lucacros/2324_Projet2A_PedaleGuitare/Hardware/img/att.ZSk6oNu2TNIRMZUWemjoR3e5RhZ518ov_QuzrdiQLX0.jpg

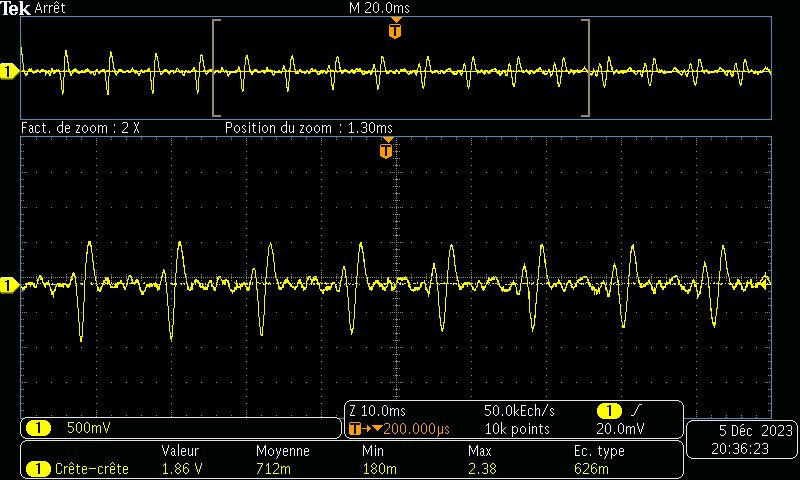
Hardware/img/att.ZSk6oNu2TNIRMZUWemjoR3e5RhZ518ov_QuzrdiQLX0.jpg
