lucacros/2324_Projet2A_PedaleGuitare/Hardware/img/Buffer button.png

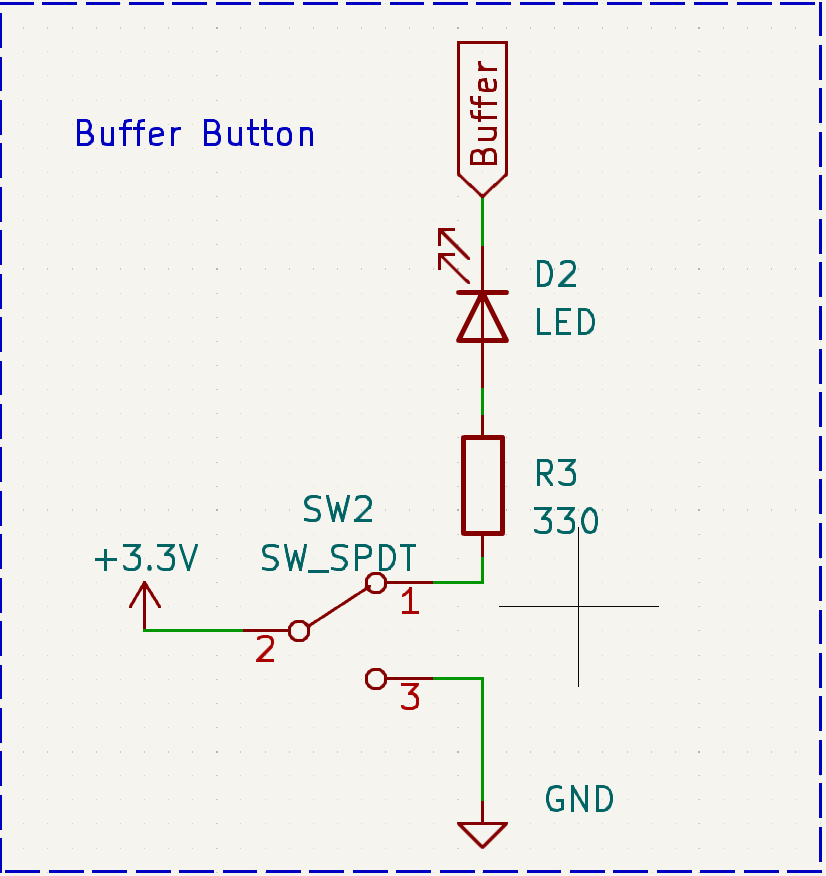
Hardware/img/Buffer button.png
