lucacros/2324_Projet2A_PedaleGuitare/Hardware/img/codecPins.png

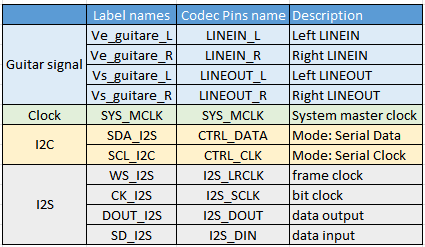
Hardware/img/codecPins.png
