lucacros/2324_Projet2A_PedaleGuitare/Hardware/img/Jack.png

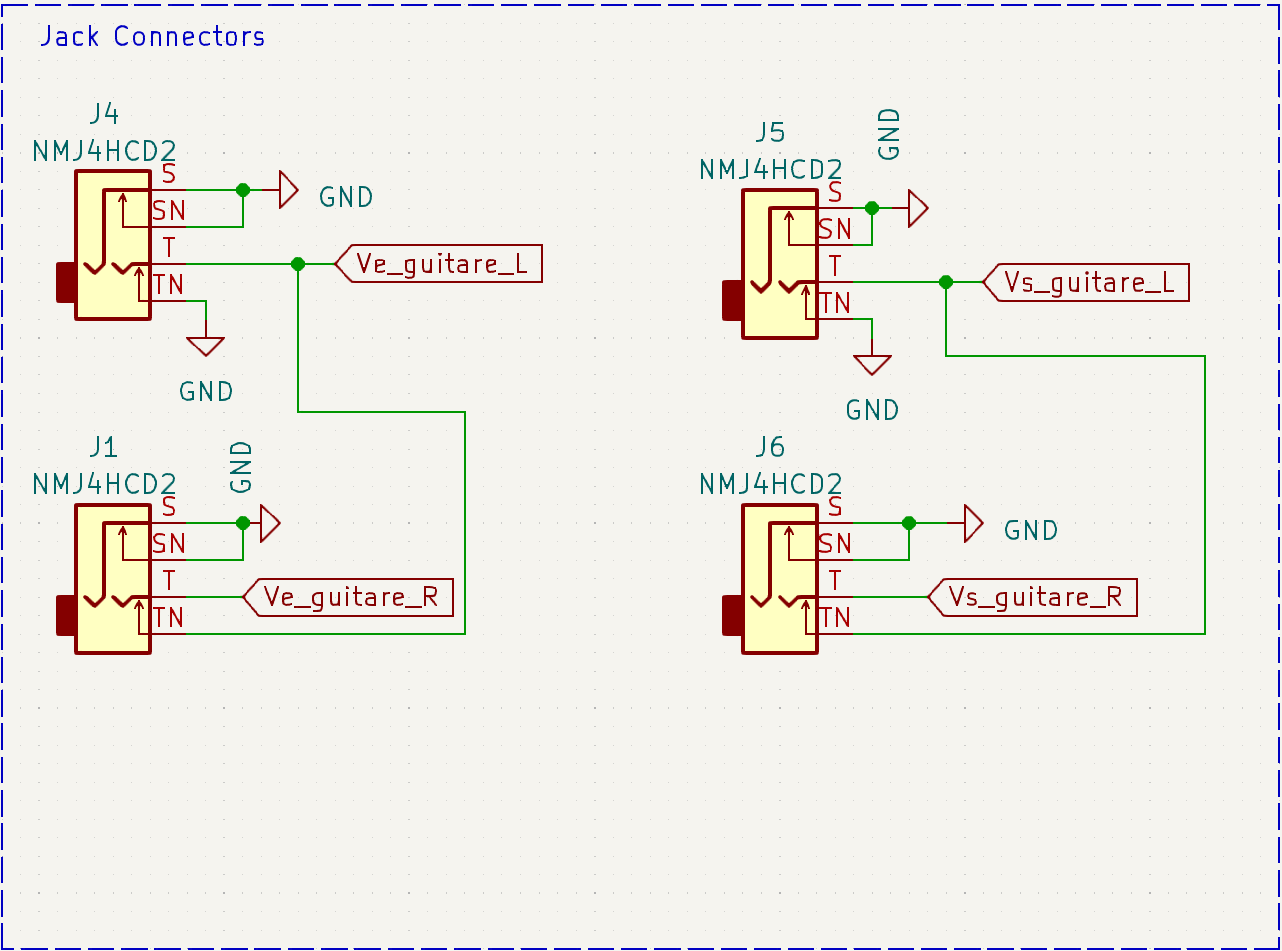
Hardware/img/Jack.png
