lucacros/2324_Projet2A_PedaleGuitare/Hardware/img/Linear_supply_vdda.png

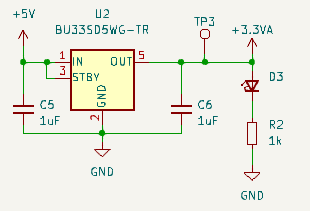
Hardware/img/Linear_supply_vdda.png
