lucacros/2324_Projet2A_PedaleGuitare/Hardware/img/powerCodec2.png

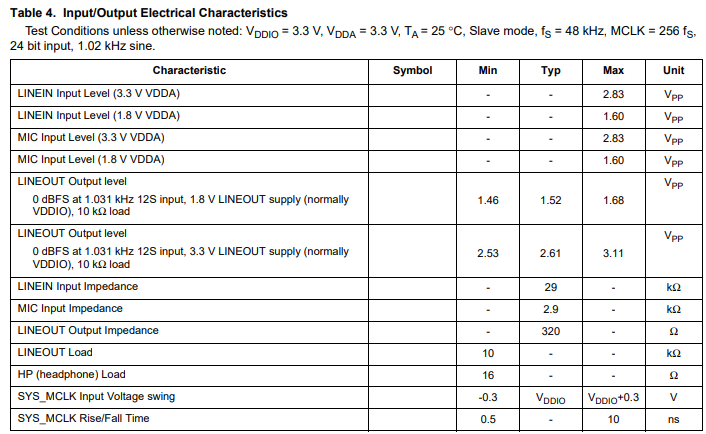
Hardware/img/powerCodec2.png
