lucacros/2324_Projet2A_PedaleGuitare/Hardware/img/ram.png

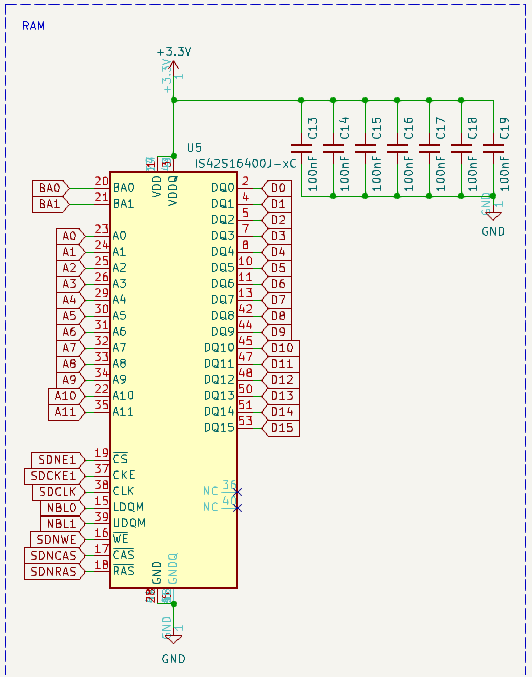
Hardware/img/ram.png
