lucacros/2324_Projet2A_PedaleGuitare/Hardware/img/STM32.png

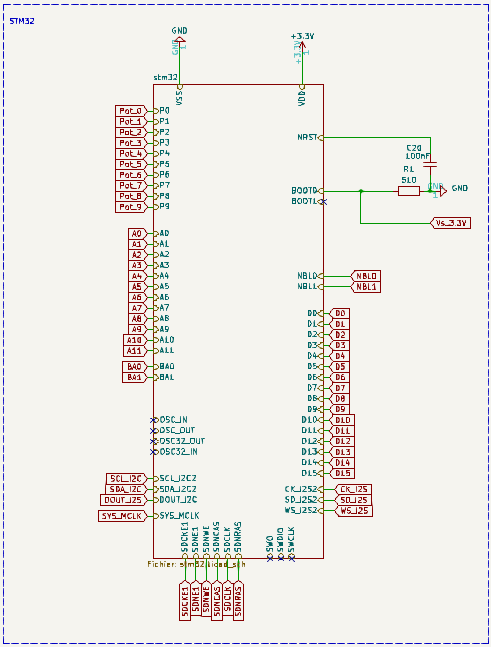
Hardware/img/STM32.png
